tomcircuit/Apple2PicoPSU/Media/installed_outside.jpg

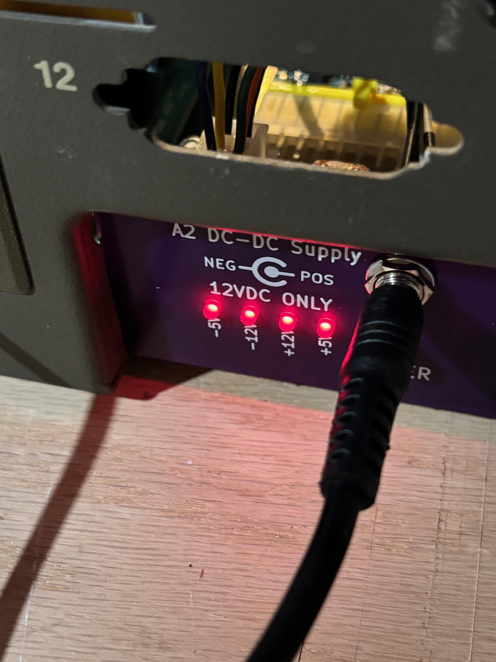
Media/installed_outside.jpg
